miguel-isidro05/Open-Ratio-Fluorimeter/Firmware/IO_Rodeo_PyBadge/reference_upstream/README.md

## Multi-channel Open Colorimeter Firmware (prototype)

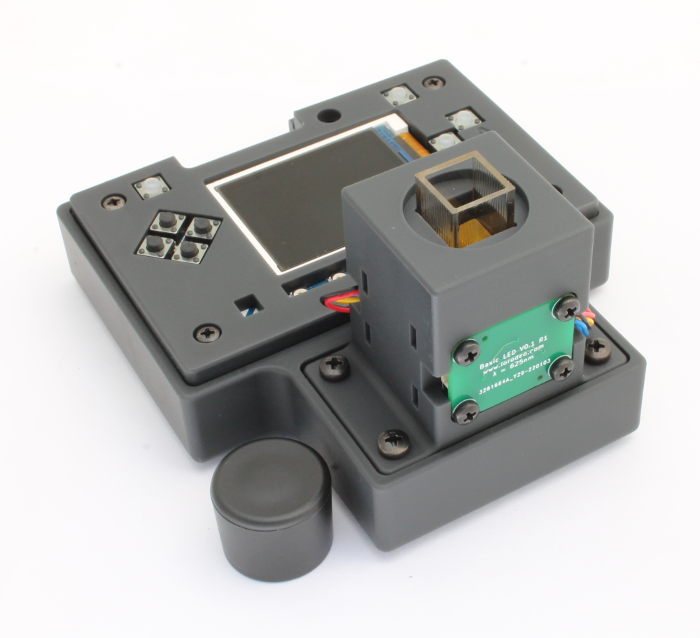
[picture p1: Firmware/IO_Rodeo_PyBadge/reference_upstream/images/open_colorimeter.png]
Open colorimeter


Firmware (circuitpython) for the open colorimeter with the AS7341 10-Channel
Light/Color Sensor.

### Requirements

* circuitpython >= 7.32
* adafruit_bitmap_font
* adafruit_bus_device
* adafruit_display_text
* adatfruit_itertools
* adafruit_as7341
* adafruit_register

### Installation

* Copy the code.py and all the .py files in src file to the CIRCUITPY drive associated with
your feather development board.

* Copy assets folder to the CIRCUITPY drive

* Copy the following libraries from the circuitpython bundle to CIRCUITPY/lib

    - adafruit_bitmap_font
    - adafruit_bus_device
    - adafruit_display_text
    - adafruit_display_shapes
    - adatfruit_itertools
    - adafruit_as7341
