miguel-isidro05/Open-Ratio-Fluorimeter/Hardware/Electronics/Power/Energy/cortadora_laser_v5_energy/README.md

# Energy para corte láser

Conjunto de salida asociado al flujo de corte láser: cobre frontal, borde, perforaciones PTH y NPTH y archivo de trabajo Gerber.

La etiqueta `v5` proviene del nombre original de la carpeta. No implica por sí sola que el esquema eléctrico tenga una revisión formal V5.
