miguel-isidro05/Open-Ratio-Fluorimeter/Hardware/Electronics/Power/Energy/flatcam_files/README.md

# Energy V1

Primera preparación de fabricación. Conserva Gerber, perforaciones, mapas de altura y varias revisiones de las rutas de pista y taladro.
