miguel-isidro05/Open-Ratio-Fluorimeter/Hardware/Electronics/Power/Energy/flatcam_files_v2/README.md

# Energy V2

Segunda preparación de fabricación. Incluye proyecto FlatCAM, Gerber, perforaciones, mapas y rutas separadas para pista y taladro.
