miguel-isidro05/Open-Ratio-Fluorimeter/Hardware/Electronics/Power/README.md

# Alimentación

La carpeta [`Energy/`](Energy/) conserva el proyecto de alimentación y sus salidas de fabricación.
