miguel-isidro05/Open-Ratio-Fluorimeter/Hardware/Electronics/Excitation/flatcam_files_v4/README.md

# Excite V4

Cuarta preparación de mecanizado. Contiene rutas separadas para borde, pista y taladro, además del proyecto FlatCAM y su mapa.

Esta carpeta corresponde a la ruta CNC. La variante para corte láser se conserva en `flatcam_files_v4_laser`.
