miguel-isidro05/Open-Ratio-Fluorimeter/Hardware/Electronics/Excitation/flatcam_files_v2/README.md

# Excite V2

Segunda preparación de fabricación. Separa las rutas `pista_v1.nc` y `taladro_v2.nc` y conserva los Gerber que sirvieron como entrada.

Verifica el diámetro de herramienta y el cero de máquina antes de reutilizar los archivos NC.
