miguel-isidro05/Open-Ratio-Fluorimeter/Hardware/Electronics/Excitation/flatcam_files_v4_laser/README.md

# Excite V4 para láser

Adaptación de la cuarta iteración al flujo de fabricación con láser. Contiene DXF para corte y pistas, SVG para taladro y los Gerber de referencia.

No asumas que las compensaciones de ancho de corte son iguales a las de la ruta CNC.
