miguel-isidro05/Open-Ratio-Fluorimeter/Hardware/Electronics/Excitation/flatcam_files_v3/README.md

# Excite V3

Tercera preparación de fabricación. Incluye `pista1_v3.nc`, `taladro1_v3.nc`, un mapa de altura y el modelo `Excite_V3.step`.

El STEP permite revisar el volumen de la placa y su relación con la carcasa, pero no sustituye la verificación del ensamblaje real.
