miguel-isidro05/Open-Ratio-Fluorimeter/Experiments/Arduino_Mega_4_LED/data/sessions/20260908_172816_751cb62c/telemetry.csv

received_at | sequence | millis | gain | integration_time | page | 415 | 445 | 480 | 515 | 555 | 590 | 630 | 680 | nir | clear
2026-09-08T22:28:29.720805+00:00 | 4 | 1421 | 128x | 100ms | 0 | 6 | 14 | 18 | 22 | 6 | 14 | 18 | 22 | 20 | 102
2026-09-08T22:28:30.070698+00:00 | 5 | 1775 | 128x | 100ms | 0 | 6 | 14 | 18 | 22 | 6 | 14 | 18 | 22 | 20 | 102
2026-09-08T22:28:30.420983+00:00 | 6 | 2129 | 128x | 100ms | 0 | 6 | 14 | 18 | 22 | 6 | 14 | 18 | 22 | 20 | 102
2026-09-08T22:28:30.795023+00:00 | 7 | 2484 | 128x | 100ms | 0 | 5 | 14 | 18 | 22 | 6 | 14 | 18 | 22 | 20 | 102
2026-09-08T22:28:31.145663+00:00 | 8 | 2838 | 128x | 100ms | 0 | 6 | 14 | 18 | 22 | 6 | 14 | 18 | 23 | 20 | 102
2026-09-08T22:28:31.495292+00:00 | 9 | 3192 | 128x | 100ms | 1 | 6 | 14 | 18 | 22 | 6 | 14 | 18 | 22 | 20 | 102
2026-09-08T22:28:31.845790+00:00 | 10 | 3547 | 128x | 100ms | 1 | 6 | 14 | 18 | 22 | 6 | 14 | 18 | 22 | 20 | 102
2026-09-08T22:28:32.195865+00:00 | 11 | 3902 | 128x | 100ms | 1 | 5 | 14 | 18 | 22 | 6 | 14 | 18 | 22 | 20 | 102
2026-09-08T22:28:32.570440+00:00 | 12 | 4256 | 128x | 100ms | 1 | 6 | 14 | 18 | 22 | 6 | 14 | 18 | 22 | 20 | 102
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
