miguel-isidro05/Open-Ratio-Fluorimeter/Experiments/Arduino_Mega_4_LED/data/sessions/20260908_190211_2c0ea6f4/telemetry.csv

received_at | sequence | millis | gain | integration_time | page | 415 | 445 | 480 | 515 | 555 | 590 | 630 | 680 | nir | clear
2026-09-09T00:06:24.851919+00:00 | 1 | 240 | 128x | 100ms | 0 | 0 | 0 | 0 | 1 | 0 | 0 | 0 | 1 | 0 | 4
2026-09-09T00:06:25.112967+00:00 | 2 | 499 | 128x | 100ms | 0 | 0 | 0 | 0 | 1 | 0 | 0 | 0 | 1 | 0 | 4
2026-09-09T00:06:25.369549+00:00 | 3 | 758 | 128x | 100ms | 0 | 0 | 0 | 0 | 1 | 0 | 0 | 0 | 1 | 0 | 4
2026-09-09T00:06:25.632934+00:00 | 4 | 1017 | 128x | 100ms | 0 | 0 | 0 | 0 | 1 | 0 | 0 | 0 | 1 | 0 | 4
2026-09-09T00:06:25.889430+00:00 | 5 | 1276 | 128x | 100ms | 0 | 0 | 0 | 0 | 1 | 0 | 0 | 0 | 1 | 0 | 4
2026-09-09T00:06:26.145566+00:00 | 6 | 1536 | 128x | 100ms | 0 | 0 | 0 | 0 | 1 | 0 | 0 | 0 | 1 | 0 | 4
2026-09-09T00:06:26.408955+00:00 | 7 | 1795 | 128x | 100ms | 0 | 0 | 0 | 0 | 1 | 0 | 0 | 0 | 1 | 0 | 5
2026-09-09T00:06:26.666065+00:00 | 8 | 2054 | 128x | 100ms | 0 | 0 | 0 | 0 | 1 | 0 | 0 | 0 | 1 | 0 | 5
2026-09-09T00:06:26.921249+00:00 | 9 | 2314 | 128x | 100ms | 0 | 0 | 0 | 0 | 1 | 0 | 0 | 0 | 1 | 0 | 5
2026-09-09T00:06:27.185760+00:00 | 10 | 2572 | 128x | 100ms | 0 | 0 | 0 | 0 | 1 | 0 | 0 | 0 | 1 | 0 | 4
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
