miguel-isidro05/Open-Ratio-Fluorimeter/Experiments/Arduino_Mega_4_LED/data/sessions/20260908_194314_809bbbcd/telemetry.csv

received_at | sequence | millis | gain | integration_time | page | 415 | 445 | 480 | 515 | 555 | 590 | 630 | 680 | nir | clear
2026-09-09T00:44:26.327290+00:00 | 1 | 670 | 128x | 300ms | 0 | 0 | 0 | 0 | 0 | 0 | 1 | 1 | 0 | 0 | 6
2026-09-09T00:44:27.014738+00:00 | 2 | 1360 | 128x | 300ms | 0 | 0 | 0 | 0 | 0 | 0 | 1 | 1 | 0 | 0 | 6
2026-09-09T00:44:27.709798+00:00 | 3 | 2051 | 128x | 300ms | 0 | 0 | 0 | 0 | 0 | 0 | 2 | 1 | 0 | 0 | 6
2026-09-09T00:44:28.398941+00:00 | 4 | 2741 | 128x | 300ms | 0 | 0 | 0 | 0 | 0 | 1 | 2 | 1 | 0 | 0 | 6
2026-09-09T00:44:29.087173+00:00 | 5 | 3431 | 128x | 300ms | 1 | 0 | 0 | 0 | 0 | 1 | 1 | 0 | 0 | 0 | 6
2026-09-09T00:44:29.775211+00:00 | 6 | 4121 | 128x | 300ms | 1 | 0 | 0 | 0 | 0 | 0 | 1 | 1 | 0 | 0 | 6
2026-09-09T00:44:30.470258+00:00 | 7 | 4811 | 128x | 300ms | 1 | 0 | 0 | 0 | 0 | 1 | 1 | 1 | 0 | 0 | 6
2026-09-09T00:44:31.158981+00:00 | 8 | 5501 | 128x | 300ms | 1 | 0 | 0 | 0 | 0 | 0 | 1 | 1 | 0 | 0 | 6
2026-09-09T00:44:31.847294+00:00 | 9 | 6191 | 128x | 300ms | 0 | 0 | 0 | 0 | 0 | 1 | 1 | 1 | 0 | 0 | 6
2026-09-09T00:44:32.534510+00:00 | 10 | 6881 | 128x | 300ms | 0 | 0 | 0 | 0 | 0 | 0 | 2 | 1 | 0 | 0 | 6
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
