miguel-isidro05/Open-Ratio-Fluorimeter/Experiments/Arduino_Mega_4_LED/data/sessions/20260911_092644_e69f3f95/telemetry.csv

received_at | sequence | millis | gain | integration_time | page | 415 | 445 | 480 | 515 | 555 | 590 | 630 | 680 | nir | clear
2026-09-11T14:26:54.062586+00:00 | 3 | 2051 | 128x | 300ms | 0 | 0 | 0 | 0 | 0 | 2 | 2 | 1 | 0 | 0 | 6
2026-09-11T14:26:54.750629+00:00 | 4 | 2741 | 128x | 300ms | 0 | 0 | 0 | 0 | 0 | 2 | 2 | 1 | 0 | 0 | 6
2026-09-11T14:26:55.438541+00:00 | 5 | 3431 | 128x | 300ms | 1 | 0 | 0 | 0 | 0 | 0 | 0 | 0 | 0 | 0 | 0
2026-09-11T14:26:56.126563+00:00 | 6 | 4121 | 128x | 300ms | 1 | 0 | 0 | 0 | 0 | 0 | 0 | 0 | 0 | 0 | 0
2026-09-11T14:26:56.822367+00:00 | 7 | 4812 | 128x | 300ms | 1 | 0 | 0 | 0 | 0 | 0 | 0 | 0 | 0 | 0 | 0
2026-09-11T14:26:57.510221+00:00 | 8 | 5502 | 128x | 300ms | 1 | 0 | 0 | 0 | 0 | 0 | 0 | 0 | 0 | 0 | 0
2026-09-11T14:26:58.206462+00:00 | 9 | 6193 | 128x | 300ms | 0 | 0 | 0 | 0 | 0 | 0 | 0 | 0 | 0 | 0 | 0
2026-09-11T14:26:58.894249+00:00 | 10 | 6883 | 128x | 300ms | 0 | 0 | 0 | 0 | 0 | 0 | 0 | 0 | 0 | 0 | 0
2026-09-11T14:26:59.581789+00:00 | 11 | 7573 | 128x | 300ms | 0 | 0 | 0 | 0 | 0 | 0 | 0 | 0 | 0 | 0 | 0
2026-09-11T14:26:59.974930+00:00 | 12 | 7966 | 128x | 50ms | 0 | 0 | 0 | 0 | 0 | 0 | 0 | 0 | 0 | 0 | 0
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
