miguel-isidro05/Open-Ratio-Fluorimeter/Software/IO_Rodeo_TSL2591_GUI/v1.0/upch_gui/__main__.py

"""Punto de entrada de la aplicación."""

import sys

from PyQt6.QtWidgets import QApplication

from .main_window import MainWindow


def main() -> int:
    application = QApplication(sys.argv)
    application.setApplicationName("UPCH GUI")
    window = MainWindow()
    window.show()
    return application.exec()


if __name__ == "__main__":
    raise SystemExit(main())
