miguel-isidro05/Open-Ratio-Fluorimeter/Software/Arduino_Mega_AS7341_GUI/v1.0/desktop_gui/session_store.py

"""Persistencia local atómica; el archivo anterior sobrevive a una escritura fallida."""
import json
import os
import tempfile
from pathlib import Path


def atomic_json(path, data):
    path = Path(path)
    payload = json.dumps(data, ensure_ascii=False, allow_nan=False, indent=2)
    path.parent.mkdir(parents=True, exist_ok=True)
    temporary = None
    try:
        with tempfile.NamedTemporaryFile(mode='w', encoding='utf-8', dir=path.parent,
                                         prefix=path.name + '.', suffix='.tmp', delete=False) as output:
            temporary = Path(output.name)
            output.write(payload)
            output.flush()
            os.fsync(output.fileno())
        os.replace(temporary, path)
    finally:
        if temporary is not None and temporary.exists():
            temporary.unlink()
